rambip/splitboard/code/keyboard/config.h

// ----------------------
#pragma once           // do not
#include "OS_layouts.h"// touch !
// ----------------------


// os settings:
// #define AZERTY
// #define QWERTY



/*
 _        _ __   _____  _   _ _____ 
| |      / \\ \ / / _ \| | | |_   _|
| |     / _ \\ V / | | | | | | | |  
| |___ / ___ \| || |_| | |_| | | |  
|_____/_/   \_\_| \___/ \___/  |_|  

if your're looking for a key and don't know its name,
look inside OS_layouts.h
*/
                                    
const char _base_layer[36] PROGMEM = 
{
    // TODO: debug "`" and "^" key 
'\t','b','é','p','o','w',      '`','v','d','l','j',C_BS,
C_ES,'a','u','i','e',',',      'c','t','s','r','n','m',
C_DEL ,'z','y','x','.','\'',     'k','q','g','h','f','\n',
};

const char _shift_layer[36] PROGMEM = 
{
'\t','B','è','P','O','W',      0x80,'V','D','L','J',C_BS,
C_ES,'A','U','I','E',';',      'C','T','S','R','N','M',
C_DEL ,'Z','Y','X',':','\"',     'K','Q','G','H','F','\n',
};

const char _symb_layer[36] PROGMEM = 
{
    '\t', '!' ,'@','#','$','%',        '^','&','*','(',')',C_BS,
C_ES,C_LEFT, '=', '+', '-',',',              'ç','{','}','[',']','|',
    C_DEL, '?', C_HOME,C_END,'.', '\\',         0, '<', '>', '~', '/', '\\', 
};

const char _num_layer[36] PROGMEM = 
{
    '\t','1','2','3','4','5',   '6','7','8','9','0',C_BS,
    C_ES, '*', '=','+','-',',',        C_LEFT, C_DOWN, C_UP, C_RIGHT,'0', '\n',
    C_DEL, '?', 0, 0, '.', 0,       0,   '<', '>', '~', '/', 0,  
};

const char _func_layer[36] PROGMEM =
{
    '\t', C_F1, C_F2, C_F3, C_F4, C_F5, C_F6, C_F7, C_F8, C_F9, C_F10, C_BS,
    '\t', C_F1, C_F2, C_F3, C_F4, C_F5, C_F6, C_F7, C_F8, C_F9, C_F10, C_BS,
    '\t', C_F1, C_F2, C_F3, C_F4, C_F5, C_F6, C_F7, C_F8, C_F9, C_F10, C_BS,
};


// TODO: multimedia, macro layer (with strings)

/* modifiers:
 (positions for the thumbs)
| o    |  o  |  o  |  o  |  o  |    |  o  |  o  |  o  |  o  |    o   |
|  MM  |super| alt | symb|shift|    |space| num | ctrl| fn  |  macro |

 (MM=multimedia)
*/


// layering keys (to access the corresponding layers)
#define SYMB_LAYER 40
#define SHIFT_LAYER 41
#define NUM_LAYER 43
#define FUNC_LAYER 45
#define MM_LAYER 37
#define MACRO_LAYER 46

// modifiers keys (are treated after, only for the OS)
#define MODIFIER_ALT 39
#define MODIFIER_SUPER 38
#define MODIFIER_CTRL 44

// space key
#define SPACE 42
