rambip/splitboard/code/other_tests/keyboard/tests.h

const char vimrc_data[] PROGMEM = {
  0x73, 0x65, 0x74, 0x20, 0x72, 0x65, 0x6c, 0x61, 0x74, 0x69, 0x76, 0x65,
  0x6e, 0x75, 0x6d, 0x62, 0x65, 0x72, 0x0a, 0x73, 0x65, 0x74, 0x20, 0x6e,
  0x75, 0x20, 0x72, 0x6e, 0x75, 0x0a, 0x73, 0x65, 0x74, 0x20, 0x73, 0x6d,
  0x61, 0x72, 0x74, 0x69, 0x6e, 0x64, 0x65, 0x6e, 0x74, 0x0a, 0x73, 0x65,
  0x74, 0x20, 0x65, 0x78, 0x70, 0x61, 0x6e, 0x64, 0x74, 0x61, 0x62, 0x0a,
  0x73, 0x65, 0x74, 0x20, 0x73, 0x68, 0x69, 0x66, 0x74, 0x77, 0x69, 0x64,
  0x74, 0x68, 0x3d, 0x34, 0x0a, 0x73, 0x79, 0x6e, 0x74, 0x61, 0x78, 0x20,
  0x6f, 0x6e, 0x0a, 0x73, 0x65, 0x74, 0x20, 0x73, 0x70, 0x6c, 0x69, 0x74,
  0x72, 0x69, 0x67, 0x68, 0x74, 0x0a, 0x73, 0x65, 0x74, 0x20, 0x69, 0x67,
  0x6e, 0x6f, 0x72, 0x65, 0x63, 0x61, 0x73, 0x65, 0x0a, 0x0a, 0x6d, 0x61,
  0x70, 0x20, 0xe9, 0x20, 0x3c, 0x63, 0x2d, 0x77, 0x3e, 0x0a, 0x6d, 0x61,
  0x70, 0x20, 0xc9, 0x20, 0x3c, 0x63, 0x2d, 0x76, 0x3e, 0x0a, 0x0a, 0x6c,
  0x65, 0x74, 0x20, 0x6d, 0x61, 0x70, 0x6c, 0x65, 0x61, 0x64, 0x65, 0x72,
  0x3d, 0x22, 0x20, 0x22, 0x0a, 0x0a, 0x6e, 0x6d, 0x61, 0x70, 0x20, 0x3c,
  0x74, 0x61, 0x62, 0x3e, 0x20, 0x67, 0x74, 0x0a, 0x6d, 0x61, 0x70, 0x20,
  0x3c, 0x73, 0x69, 0x6c, 0x65, 0x6e, 0x74, 0x3e, 0x20, 0x3c, 0x73, 0x70,
  0x61, 0x63, 0x65, 0x3e, 0x76, 0x20, 0x3a, 0x74, 0x61, 0x62, 0x6e, 0x65,
  0x77, 0x20, 0x7e, 0x2f, 0x2e, 0x76, 0x69, 0x6d, 0x72, 0x63, 0x3c, 0x43,
  0x52, 0x3e, 0x0a, 0x6d, 0x61, 0x70, 0x20, 0x3c, 0x73, 0x69, 0x6c, 0x65,
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
  0x20, 0x20, 0x6b, 0x65, 0x79, 0x09, 0x3c, 0x41, 0x45, 0x30, 0x36, 0x3e,
  0x09, 0x7b, 0x09, 0x5b, 0x09, 0x36, 0x2c, 0x09, 0x61, 0x73, 0x63, 0x69,
  0x69, 0x63, 0x69, 0x72, 0x63, 0x75, 0x6d, 0x09, 0x5d, 0x7d, 0x3b, 0x0a,
  0x20, 0x20, 0x6b, 0x65, 0x79, 0x09, 0x3c, 0x41, 0x45, 0x30, 0x37, 0x3e,
  0x09, 0x7b, 0x09, 0x5b, 0x09, 0x37, 0x2c, 0x09, 0x61, 0x6d, 0x70, 0x65,
  0x72, 0x73, 0x61, 0x6e, 0x64, 0x09, 0x5d, 0x7d, 0x3b, 0x0a, 0x20, 0x20,
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
};


__FlashStringHelper* bigfile = (__FlashStringHelper*)(bigfile_data);
